nelsonii/SSR8-CAP1188/2021-12-18/DSCN8658.JPG

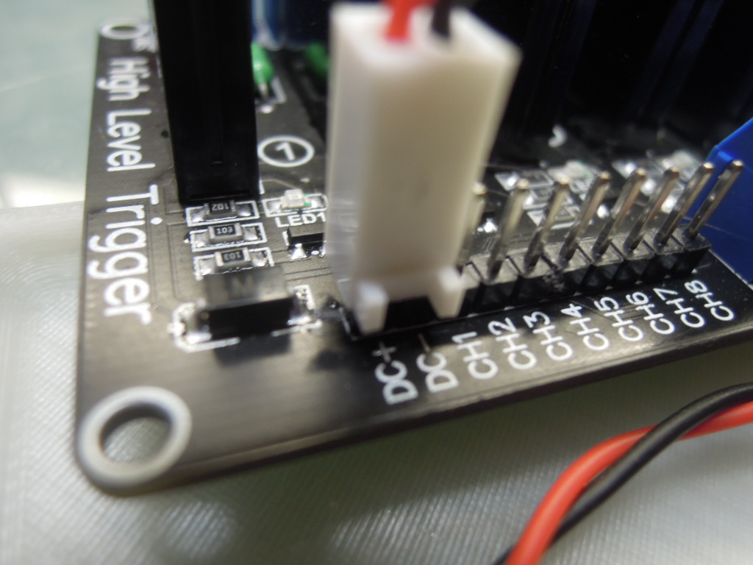
2021-12-18/DSCN8658.JPG
